Shtaiven/shockboard/cases/shockboard_v1/case_hipro_mx/case_hipro_mx_top_right.3mf

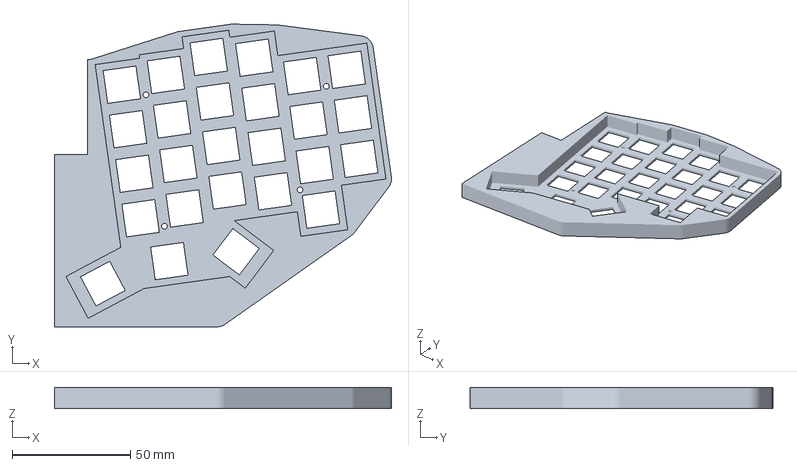
[picture p24: CAD file, 2024-06-02]
cases/shockboard_v1/case_hipro_mx/case_hipro_mx_top_right.3mf
142.4 x 128.0 x 8.90 mm
