Shtaiven/shockboard/cases/shockboard_v1/case_lopro_mx/case_lopro_mx_top.3mf

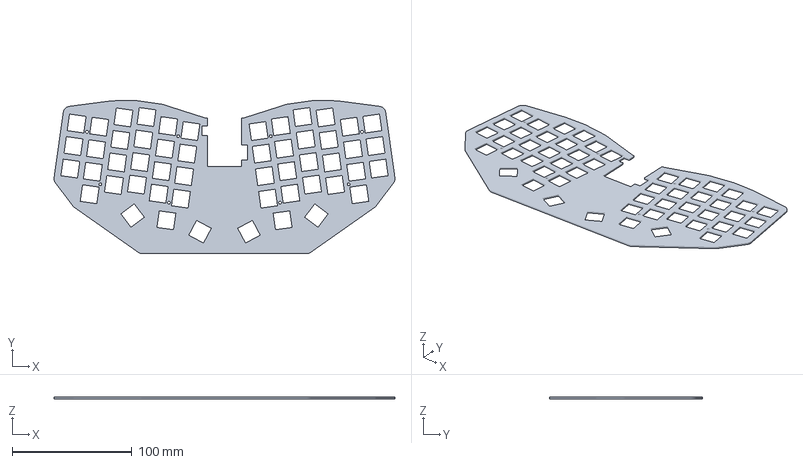
[picture p25: CAD file, 2024-06-02]
cases/shockboard_v1/case_lopro_mx/case_lopro_mx_top.3mf
284.9 x 128.0 x 1.50 mm
