Shtaiven/shockboard/cases/shockboard_v1/pcb_spacer_left.3mf

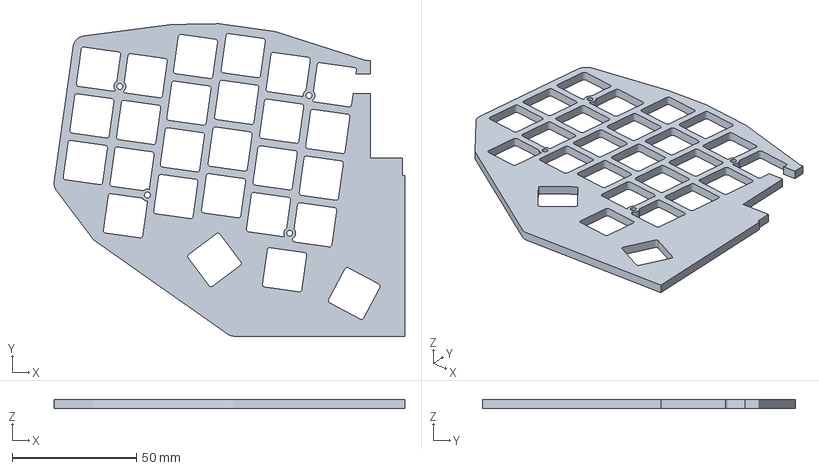
[picture p26: CAD file, 2024-06-02]
cases/shockboard_v1/pcb_spacer_left.3mf
141.4 x 126.0 x 3.50 mm
