Shtaiven/shockboard/ergogen/fairyboard_v1/output/cases/case_hipro_mx.stl

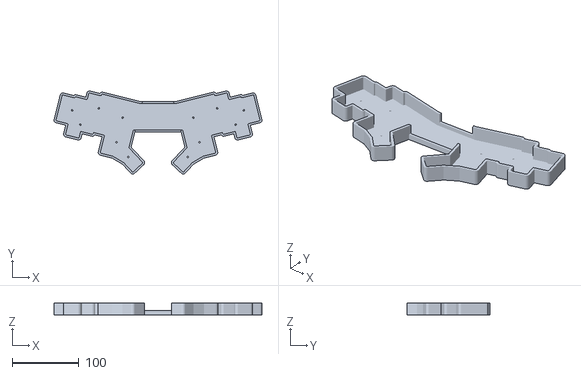
[picture p27: CAD file, 2024-10-07]
ergogen/fairyboard_v1/output/cases/case_hipro_mx.stl
311.5 x 124.3 x 17.8
