Shtaiven/shockboard/cases/fairyboard_v1/outlines/pcb_edge_support.dxf

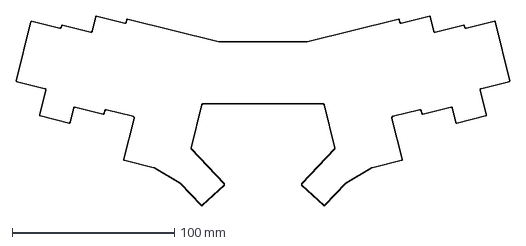
[picture p29: CAD file, 2024-10-23]
cases/fairyboard_v1/outlines/pcb_edge_support.dxf
304.0 x 116.7 mm
