Shtaiven/shockboard/cases/fairyboard_v1/simple_case/bottom_case_choc_v2.stl

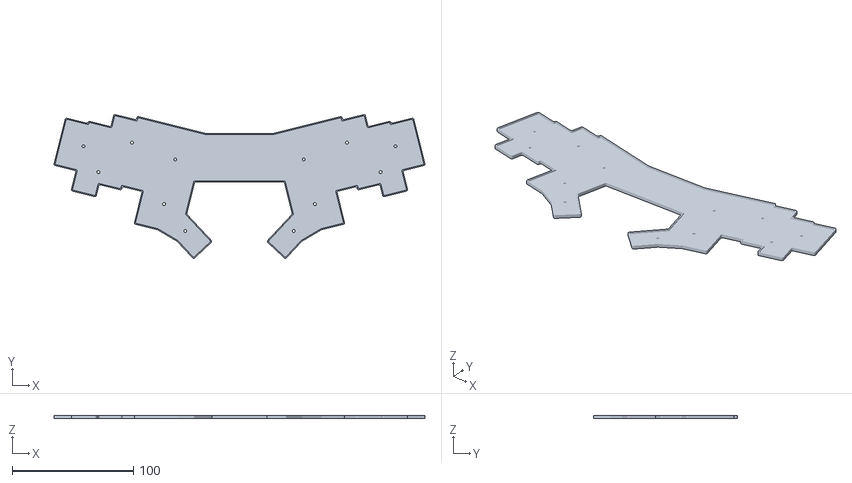
[picture p30: CAD file, 2024-11-02]
cases/fairyboard_v1/simple_case/bottom_case_choc_v2.stl
305.7 x 118.5 x 2.80
