Shtaiven/shockboard/cases/shockboard_v1/pcb_spacer.3mf

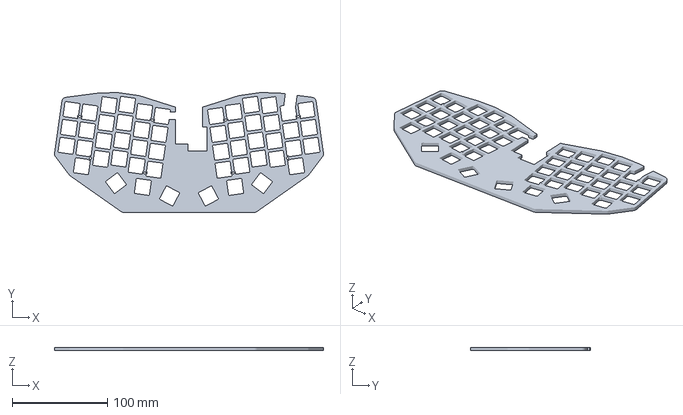
[picture p32: CAD file, 2024-06-02]
cases/shockboard_v1/pcb_spacer.3mf
282.9 x 126.0 x 3.50 mm
