Shtaiven/shockboard/ergogen/shockboard_v1/output/outlines/plate_choc.dxf

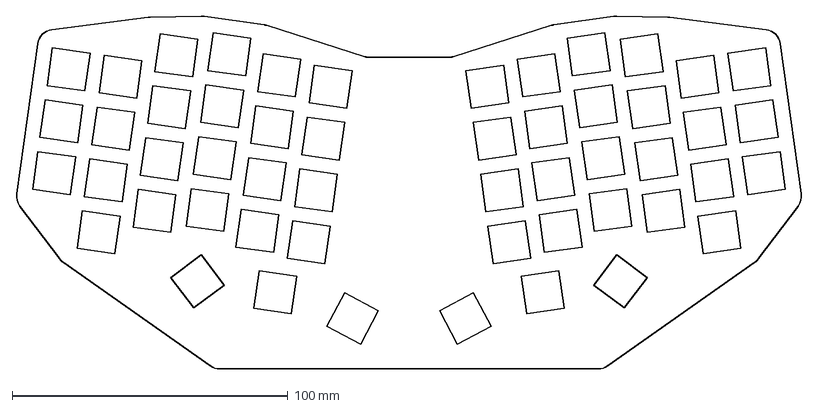
[picture p34: CAD file, 2024-05-15]
ergogen/shockboard_v1/output/outlines/plate_choc.dxf
285.2 x 128.0 mm
