Shtaiven/shockboard/cases/fairyboard_v1/outlines/m2_spacers.dxf

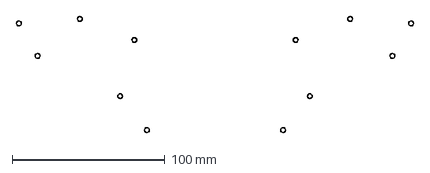
[picture p35: CAD file, 2024-10-23]
cases/fairyboard_v1/outlines/m2_spacers.dxf
260.2 x 76.1 mm
