Shtaiven/shockboard/cases/shockboard_v1/case_hipro_mx/case_hipro_mx_bottom_left.3mf

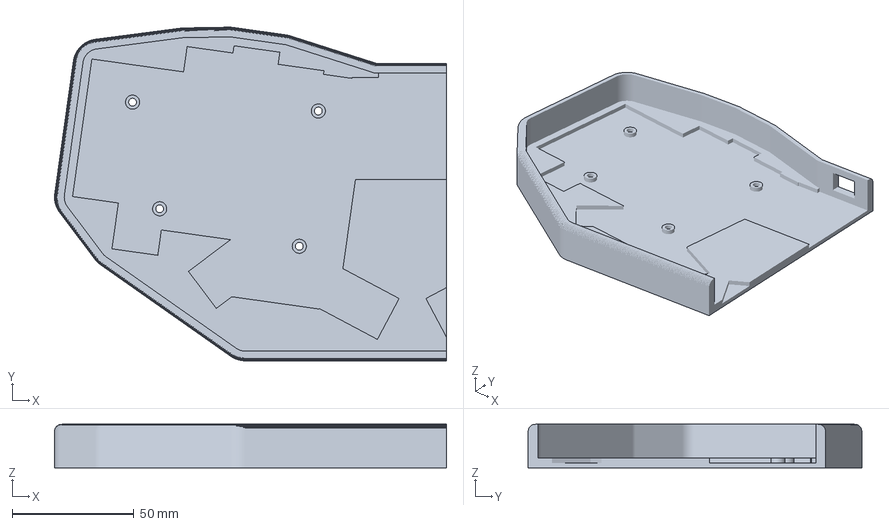
[picture p37: CAD file, 2024-06-02]
cases/shockboard_v1/case_hipro_mx/case_hipro_mx_bottom_left.3mf
160.9 x 137.0 x 18.0 mm
