Shtaiven/shockboard/cases/shockboard_v1/standoff_m2_3_5mm.3mf

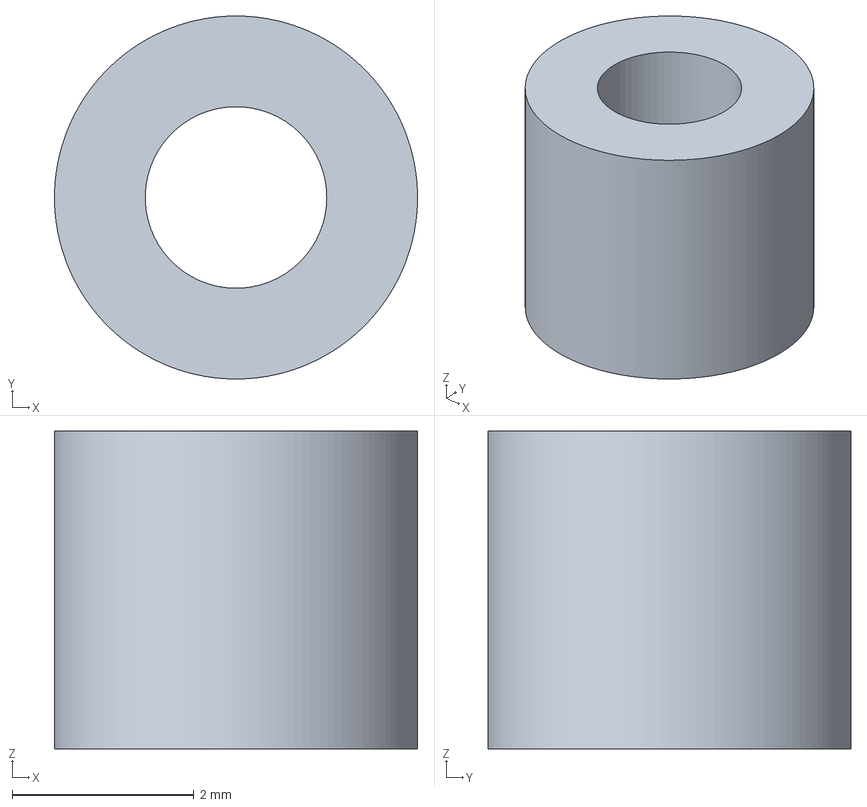
[picture p38: CAD file, 2024-05-15]
cases/shockboard_v1/standoff_m2_3_5mm.3mf
4.00 x 4.00 x 3.50 mm
