Shtaiven/shockboard/ergogen/fairyboard_v1/output/cases/testing_plate_mx.stl

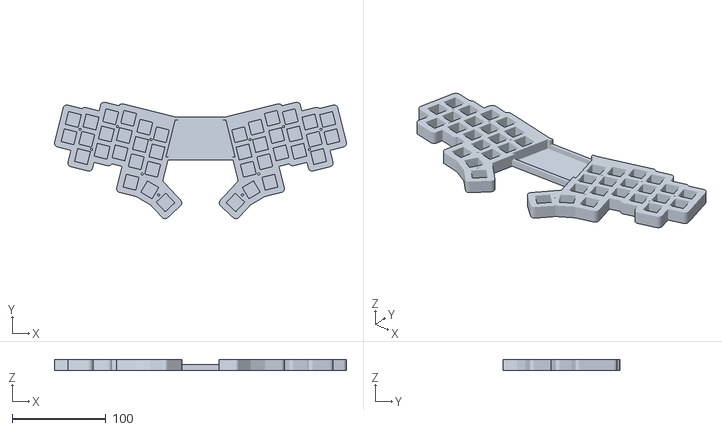
[picture p39: CAD file, 2024-10-07]
ergogen/fairyboard_v1/output/cases/testing_plate_mx.stl
311.5 x 124.3 x 11.6
