Shtaiven/shockboard/ergogen/shockboard_v1/output/outlines/wall.dxf

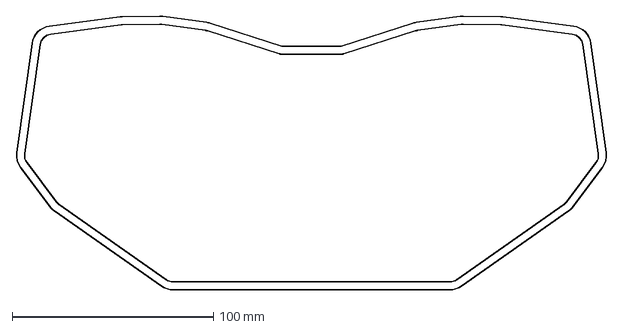
[picture p40: CAD file, 2024-05-15]
ergogen/shockboard_v1/output/outlines/wall.dxf
293.4 x 136.0 mm
