Shtaiven/shockboard/cases/fairyboard_v1/outlines/pcb_outline.dxf

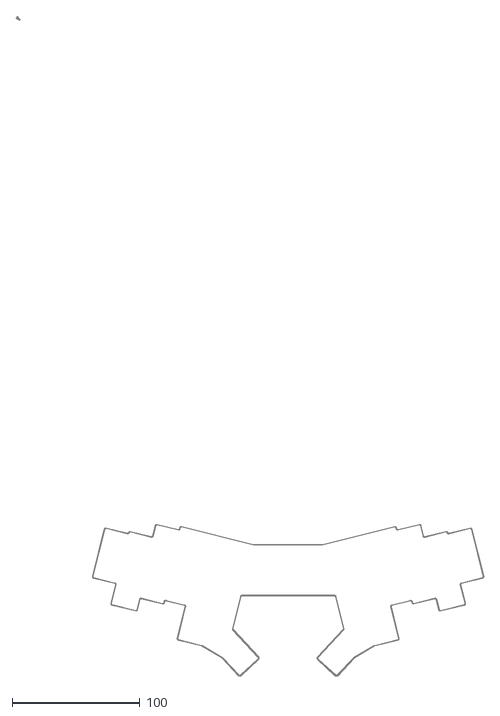
[picture p41: CAD file, 2024-10-22]
cases/fairyboard_v1/outlines/pcb_outline.dxf
365.4 x 516.2
