Shtaiven/shockboard/cases/fairyboard_v1/simple_case/top_case_choc_v2.stl

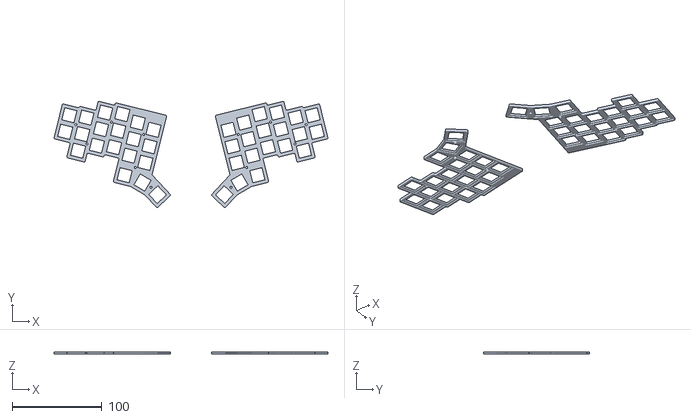
[picture p42: CAD file, 2024-10-24]
cases/fairyboard_v1/simple_case/top_case_choc_v2.stl
305.7 x 118.5 x 2.20
