Shtaiven/shockboard/cases/fairyboard_v1/slim_case/center_window_choc_with_terminal8_cutout.stl

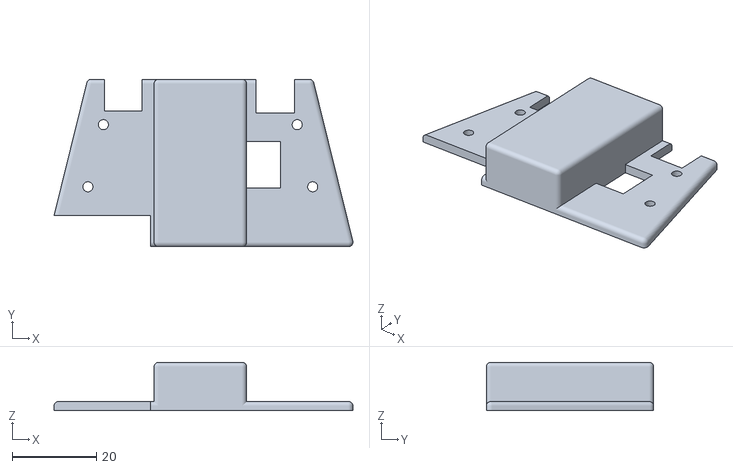
[picture p43: CAD file, 2024-12-01]
cases/fairyboard_v1/slim_case/center_window_choc_with_terminal8_cutout.stl
71.0 x 39.8 x 11.5
