Shtaiven/shockboard/cases/shockboard_v1/case_hipro_mx/case_hipro_mx_top.3mf

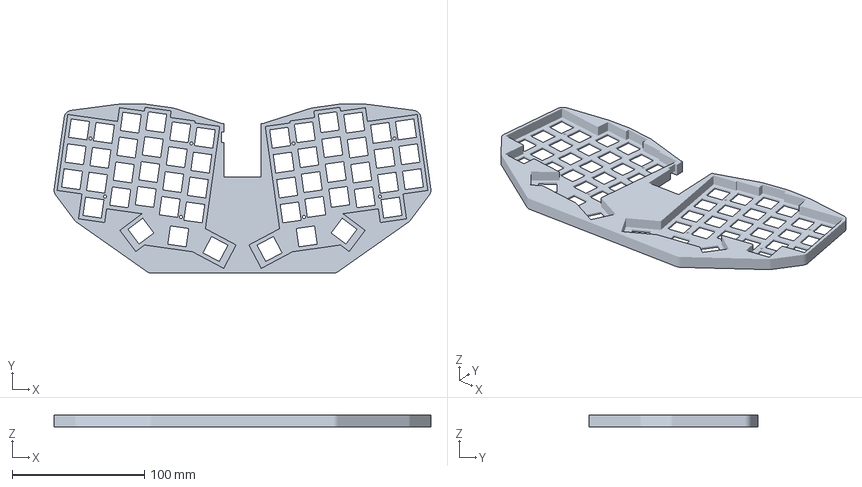
[picture p44: CAD file, 2024-06-02]
cases/shockboard_v1/case_hipro_mx/case_hipro_mx_top.3mf
284.9 x 128.0 x 8.90 mm
