Shtaiven/shockboard/ergogen/fairyboard_v1/output/cases/case_lowpro.stl

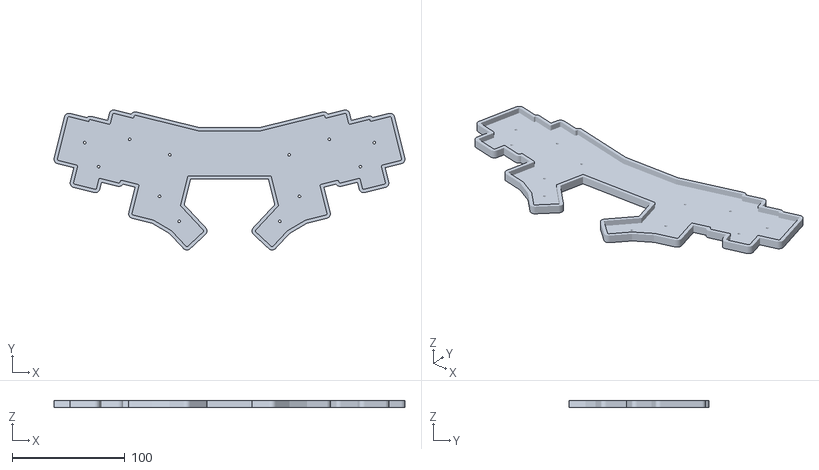
[picture p45: CAD file, 2024-10-07]
ergogen/fairyboard_v1/output/cases/case_lowpro.stl
311.5 x 124.3 x 6.60
