Shtaiven/shockboard/ergogen/shockboard_v1/output/outlines/plate_mx.dxf

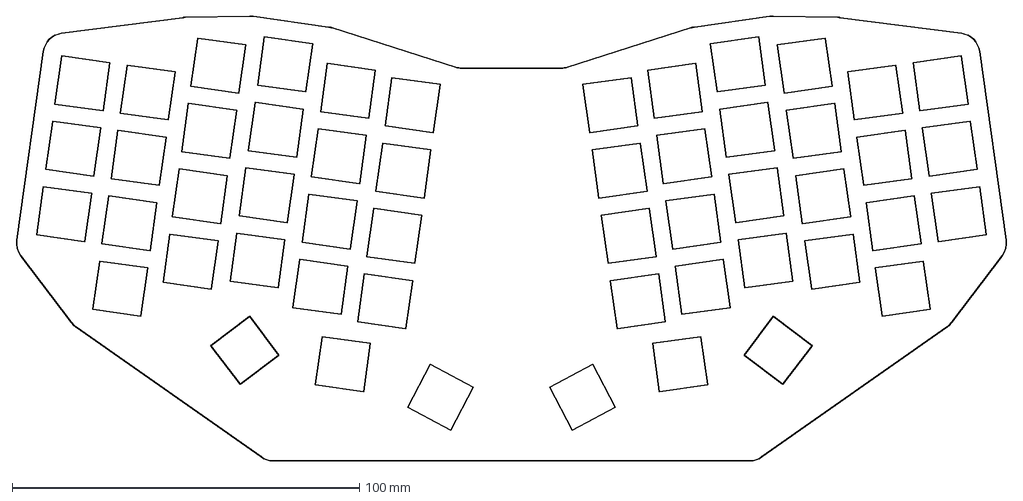
[picture p46: CAD file, 2024-05-15]
ergogen/shockboard_v1/output/outlines/plate_mx.dxf
285.2 x 128.0 mm
