Shtaiven/shockboard/cases/fairyboard_v1/outlines/board_connector.dxf

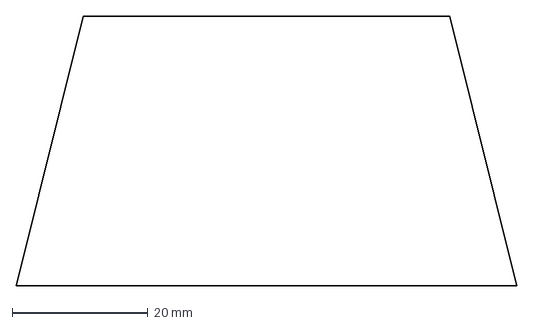
[picture p47: CAD file, 2024-10-07]
cases/fairyboard_v1/outlines/board_connector.dxf
73.9 x 39.8 mm
