Shtaiven/shockboard/cases/fairyboard_v1/simple_case/top_case_mx.stl

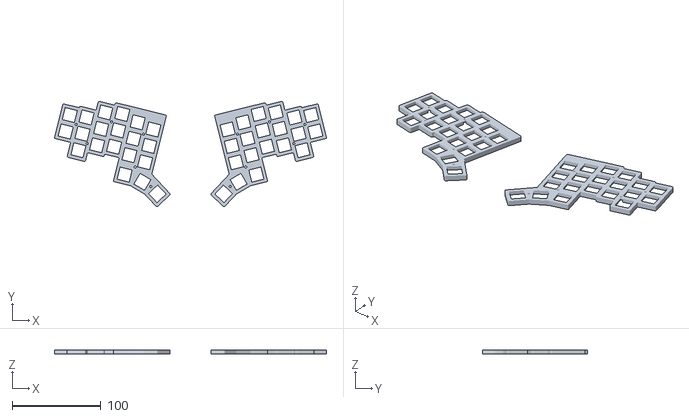
[picture p48: CAD file, 2024-10-24]
cases/fairyboard_v1/simple_case/top_case_mx.stl
305.7 x 118.5 x 5.00
