Shtaiven/shockboard/cases/shockboard_v1/case_hipro_mx/case_hipro_mx_bottom.3mf

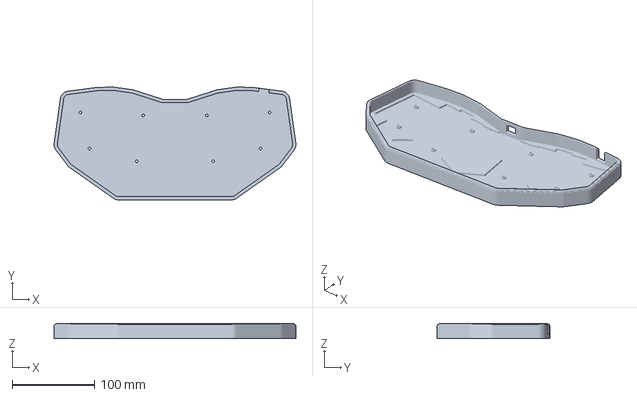
[picture p50: CAD file, 2024-06-02]
cases/shockboard_v1/case_hipro_mx/case_hipro_mx_bottom.3mf
293.9 x 137.0 x 18.0 mm
