Shtaiven/shockboard/ergogen/shockboard_v1/output/outlines/mounting_holes_outer.dxf

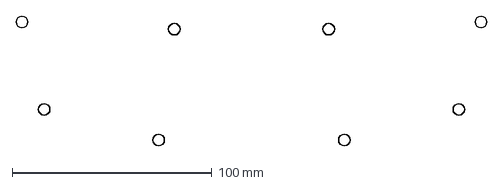
[picture p51: CAD file, 2024-05-14]
ergogen/shockboard_v1/output/outlines/mounting_holes_outer.dxf
235.6 x 64.9 mm
