Shtaiven/shockboard/cases/fairyboard_v1/outlines/board_connector_cutout.dxf

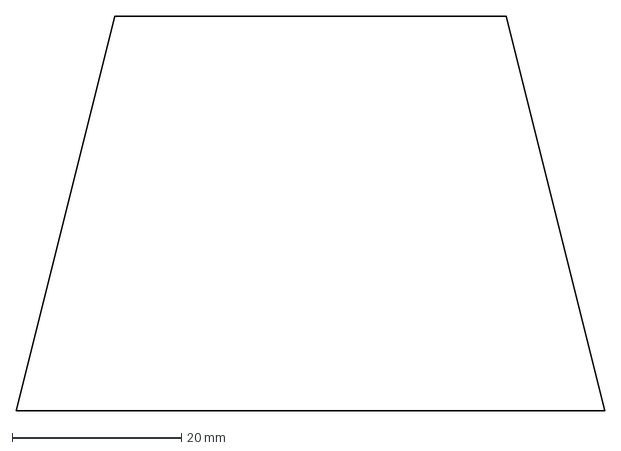
[picture p52: CAD file, 2024-10-07]
cases/fairyboard_v1/outlines/board_connector_cutout.dxf
69.6 x 46.7 mm
