Shtaiven/shockboard/ergogen/shockboard_v1/output/outlines/mounting_holes.dxf

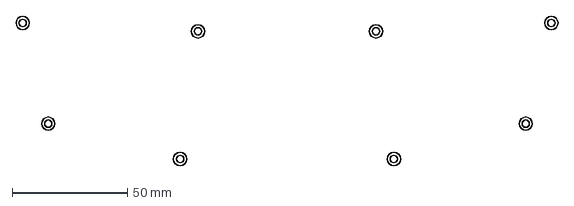
[picture p53: CAD file, 2024-05-14]
ergogen/shockboard_v1/output/outlines/mounting_holes.dxf
235.6 x 64.9 mm
