Shtaiven/shockboard/cases/fairyboard_v1/outlines/board_connector_extended.dxf

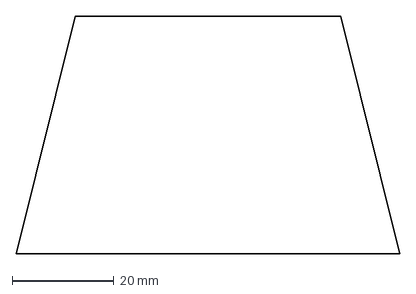
[picture p54: CAD file, 2024-10-07]
cases/fairyboard_v1/outlines/board_connector_extended.dxf
75.4 x 46.7 mm
