Shtaiven/shockboard/ergogen/shockboard_v1/output/outlines/mounting_holes_inner.dxf

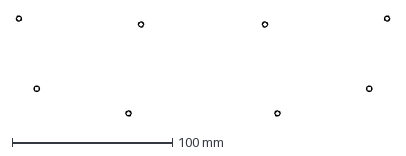
[picture p55: CAD file, 2024-05-14]
ergogen/shockboard_v1/output/outlines/mounting_holes_inner.dxf
233.0 x 62.3 mm
