Shtaiven/shockboard/cases/fairyboard_v1/outlines/plate_choc.dxf

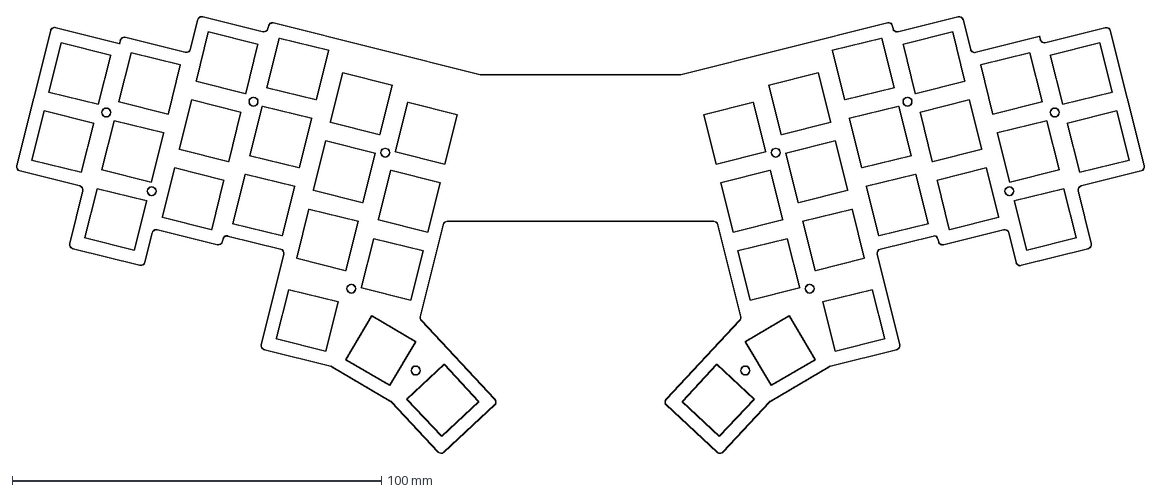
[picture p56: CAD file, 2024-10-07]
cases/fairyboard_v1/outlines/plate_choc.dxf
305.8 x 118.6 mm
