Shtaiven/shockboard/cases/fairyboard_v1/slim_case/top_case_choc_v2_right.3mf

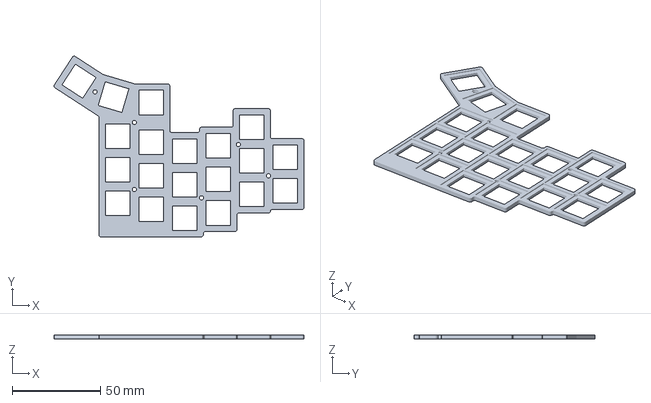
[picture p57: CAD file, 2024-11-02]
cases/fairyboard_v1/slim_case/top_case_choc_v2_right.3mf
141.6 x 102.4 x 2.20 mm
