Shtaiven/shockboard/ergogen/shockboard_v1/output/outlines/promicro_cutout.dxf

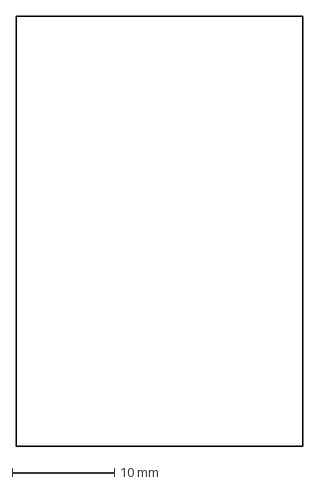
[picture p58: CAD file, 2024-05-14]
ergogen/shockboard_v1/output/outlines/promicro_cutout.dxf
28.0 x 42.0 mm
