Shtaiven/shockboard/cases/fairyboard_v1/outlines/case_outline.dxf

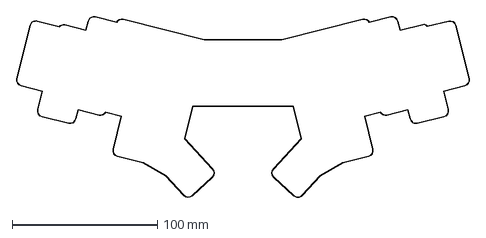
[picture p59: CAD file, 2024-10-07]
cases/fairyboard_v1/outlines/case_outline.dxf
312.4 x 125.2 mm
