Shtaiven/shockboard/ergogen/shockboard_v1/output/outlines/battery_switch_cutout.dxf

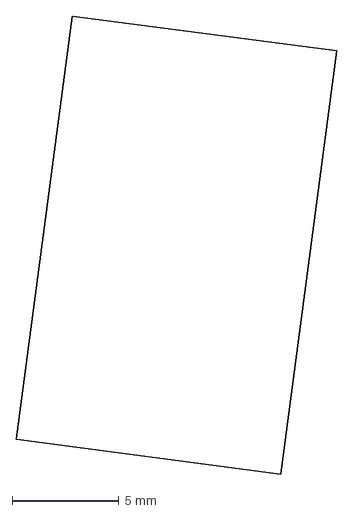
[picture p60: CAD file, 2024-05-11]
ergogen/shockboard_v1/output/outlines/battery_switch_cutout.dxf
15.0 x 21.5 mm
