Shtaiven/shockboard/cases/fairyboard_v1/outlines/m2_holes.dxf

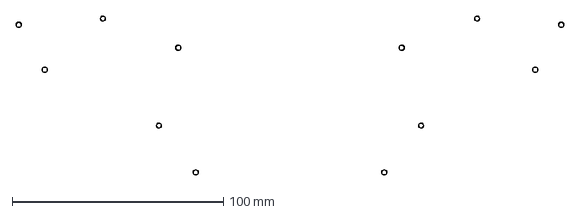
[picture p61: CAD file, 2024-10-07]
cases/fairyboard_v1/outlines/m2_holes.dxf
259.4 x 75.3 mm
