Shtaiven/shockboard/cases/fairyboard_v1/slim_case/top_case_mx_left.3mf

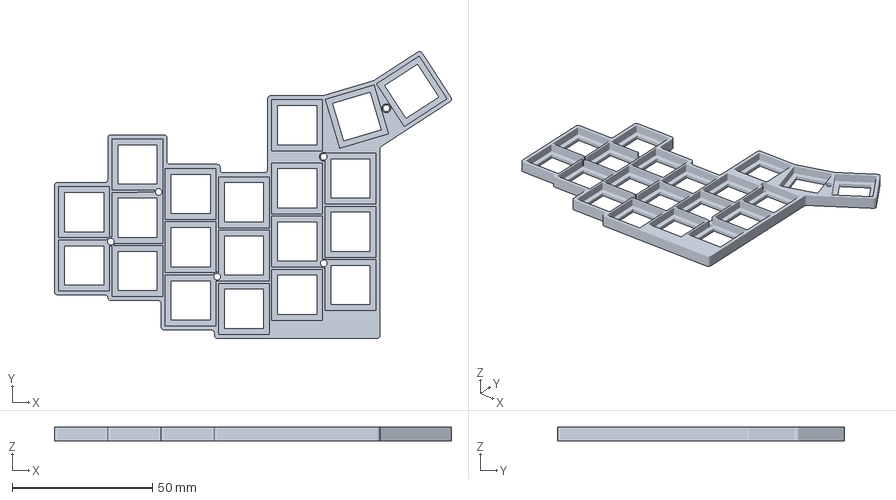
[picture p62: CAD file, 2024-11-02]
cases/fairyboard_v1/slim_case/top_case_mx_left.3mf
141.6 x 102.4 x 5.00 mm
