Shtaiven/shockboard/ergogen/shockboard_v1/output/outlines/usbc_cutout.dxf

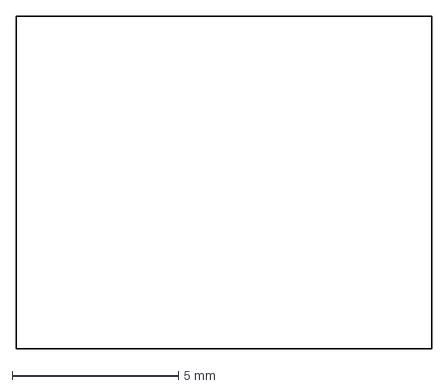
[picture p63: CAD file, 2024-05-11]
ergogen/shockboard_v1/output/outlines/usbc_cutout.dxf
12.5 x 10.0 mm
