Shtaiven/shockboard/cases/fairyboard_v1/outlines/wall.dxf

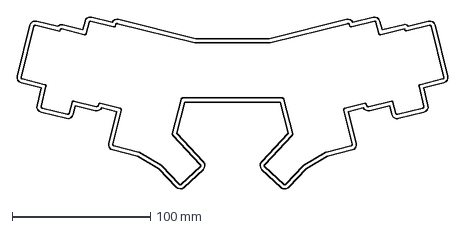
[picture p64: CAD file, 2024-10-07]
cases/fairyboard_v1/outlines/wall.dxf
312.4 x 125.2 mm
