Shtaiven/shockboard/ergogen/shockboard_v1/output/outlines/m2_holes.dxf

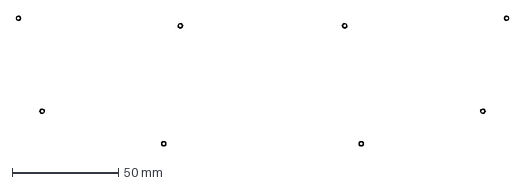
[picture p65: CAD file, 2024-05-09]
ergogen/shockboard_v1/output/outlines/m2_holes.dxf
231.8 x 61.1 mm
