Shtaiven/shockboard/cases/fairyboard_v1/outlines/plate_mx.dxf

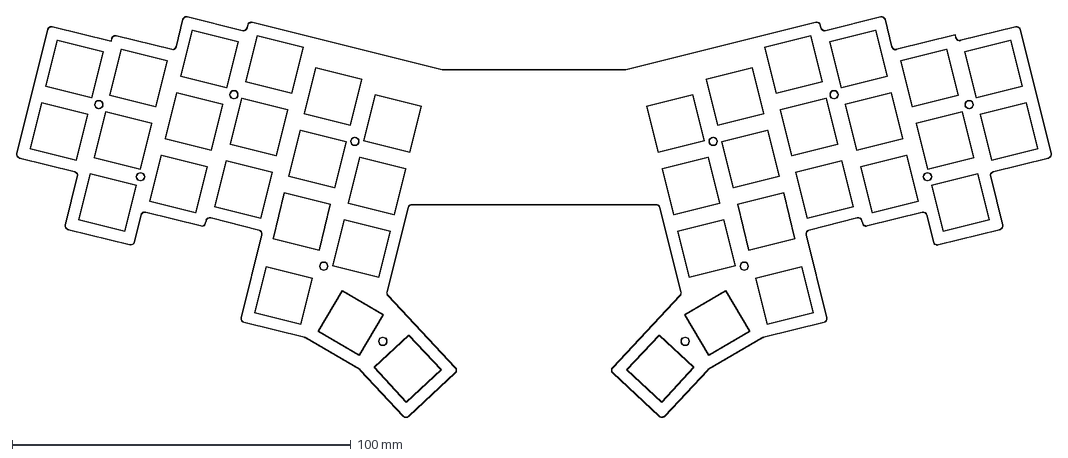
[picture p66: CAD file, 2024-10-07]
cases/fairyboard_v1/outlines/plate_mx.dxf
305.8 x 118.6 mm
