Shtaiven/shockboard/ergogen/shockboard_v1/output/outlines/board.dxf

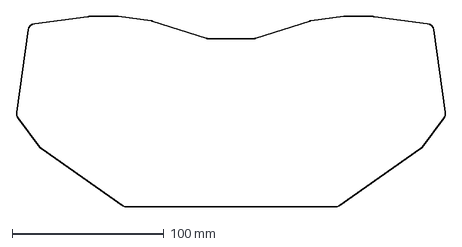
[picture p67: CAD file, 2024-04-20]
ergogen/shockboard_v1/output/outlines/board.dxf
283.1 x 126.0 mm
