Shtaiven/shockboard/cases/fairyboard_v1/outlines/board.dxf

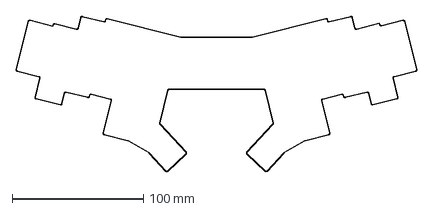
[picture p68: CAD file, 2024-09-29]
cases/fairyboard_v1/outlines/board.dxf
305.8 x 118.6 mm
