Shtaiven/shockboard/ergogen/shockboard_v1/output/outlines/case_outline.dxf

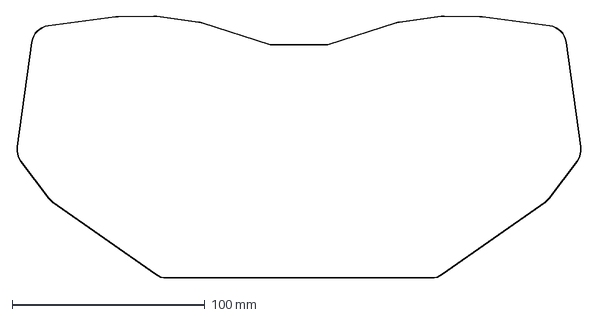
[picture p69: CAD file, 2024-04-20]
ergogen/shockboard_v1/output/outlines/case_outline.dxf
293.4 x 136.0 mm
