Shtaiven/shockboard/ergogen/shockboard_v1/output/outlines/cutouts_choc.dxf

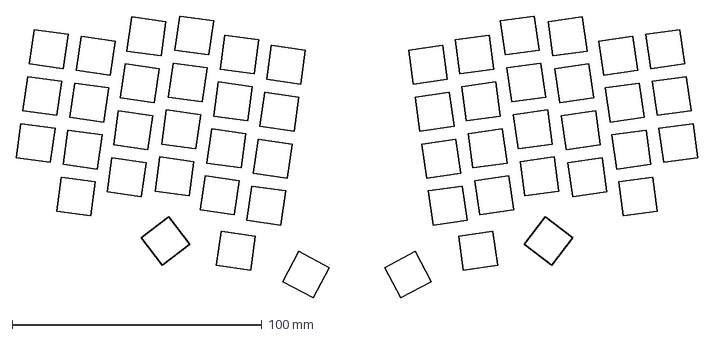
[picture p70: CAD file, 2024-03-17]
ergogen/shockboard_v1/output/outlines/cutouts_choc.dxf
273.2 x 112.9 mm
