Shtaiven/shockboard/cases/fairyboard_v1/outlines/board_raw.dxf

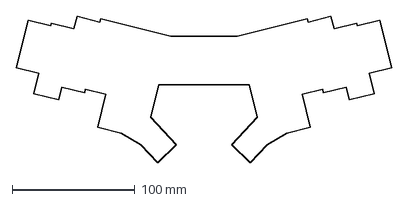
[picture p71: CAD file, 2024-09-18]
cases/fairyboard_v1/outlines/board_raw.dxf
306.0 x 119.0 mm
