Shtaiven/shockboard/ergogen/shockboard_v1/output/outlines/cutouts_mx.dxf

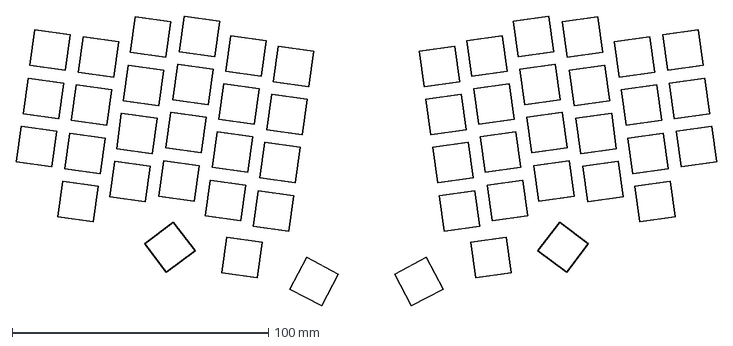
[picture p72: CAD file, 2024-03-10]
ergogen/shockboard_v1/output/outlines/cutouts_mx.dxf
273.4 x 113.2 mm
