Shtaiven/shockboard/cases/fairyboard_v1/outlines/cutouts_choc.dxf

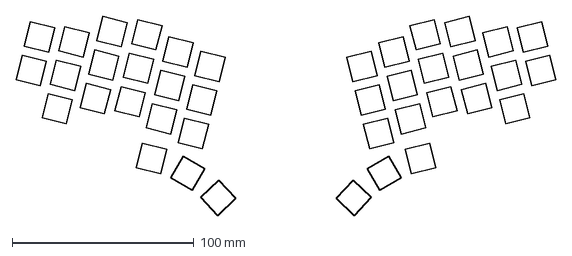
[picture p73: CAD file, 2024-08-19]
cases/fairyboard_v1/outlines/cutouts_choc.dxf
297.3 x 109.6 mm
