Shtaiven/shockboard/cases/fairyboard_v1/outlines/cutouts_mx.dxf

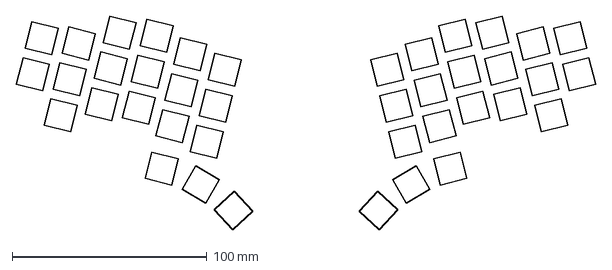
[picture p74: CAD file, 2024-08-19]
cases/fairyboard_v1/outlines/cutouts_mx.dxf
297.5 x 109.8 mm
