Shtaiven/shockboard/ergogen/shockboard-v0_3_1.yaml

#
# Define unit constants
#
units:
  # common
  SPLIT_ROTATION: -8

  # columns
  COLUMN_PINKY_STAGGER: -1u
  COLUMN_RING_STAGGER: 10.5
  COLUMN_MIDDLE_STAGGER: 3
  COLUMN_INDEX_STAGGER: -5
  COLUMN_INNER_STAGGER: -1.5
  COLUMN_EXTRA_STAGGER: 0.5u

  # thumbfan
  THUMBFAN_NEAR_ROT: 8
  THUMBFAN_HOME_ROT: -25  # TODO: adjust
  THUMBFAN_HOME_X: 10  # TODO: adjust
  THUMBFAN_HOME_Y: -1  # TODO: adjust

#
# Define key locations
#
# matrix: finger matrix (excluding thumbs)
# thumbfan: thumb keys
#
points:
  zones:
    matrix:
      columns:
        outer:
          rows:
            bottom:
            home:
            top:
        pinky:
          key.stagger: COLUMN_PINKY_STAGGER
          rows:
            bottom:
            home:
            top:
            num:
        ring:
          key.stagger: COLUMN_RING_STAGGER
          rows:
            bottom:
            home:
            top:
            num:
        middle:
          key.stagger: COLUMN_MIDDLE_STAGGER
          rows:
            bottom:
            home:
            top:
            num:
        index:
          key.stagger: COLUMN_INDEX_STAGGER
          rows:
            bottom:
            home:
            top:
            num:
        inner:
          key.stagger: COLUMN_INNER_STAGGER
          rows:
            bottom:
            home:
            top:
            num:
        extra:
          key.stagger: COLUMN_EXTRA_STAGGER
          rows:
            home:
    thumbfan:
      anchor:
        ref: matrix_middle_bottom
        shift: [0, -1.375u]
      columns:
        inner:
          key:
            rotate: 45
            shift: [-0.5u, 0]
            width: 1.25u
        near:
          key:
            splay: THUMBFAN_NEAR_ROT
        home:
          key:
            splay: THUMBFAN_HOME_ROT
            shift: [THUMBFAN_HOME_X, THUMBFAN_HOME_Y]
        far:
          key:
            shift: [THUMBFAN_HOME_X, THUMBFAN_HOME_Y]
      rows:
        thumb:
  rotate: SPLIT_ROTATION
  mirror:
    ref: matrix_inner_home
    distance: 67.5

#
# Define outlines for the plate
#
outlines:
  # cutouts for the keys to be used in plate generation
  mx_cutouts:
    - what: rectangle
      where: true
      asym: source
      size: 14
      bound: false
